matteodv99tn/MDM-Homework/Images/10-040.jpg

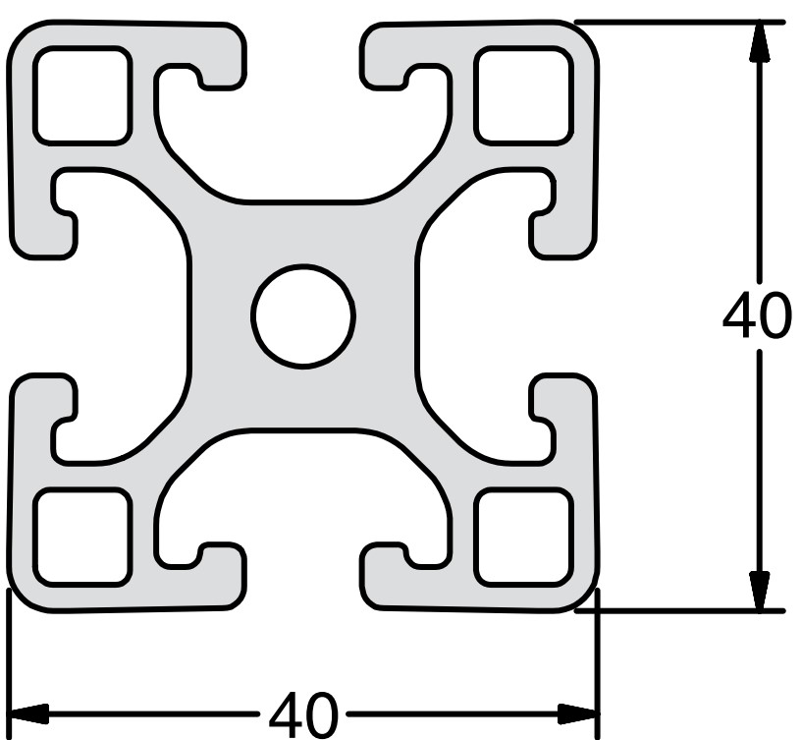
Images/10-040.jpg
