matteodv99tn/MDM-Homework/Images/10-080.jpg

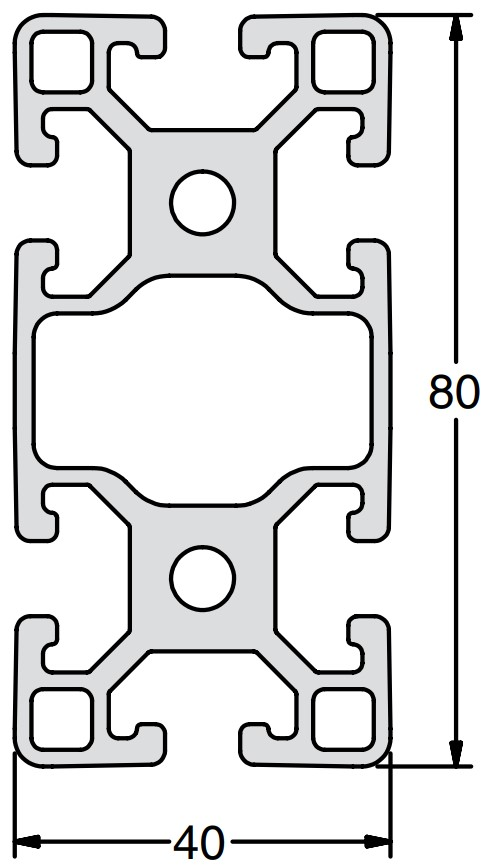
Images/10-080.jpg
