matteodv99tn/MDM-Homework/Images/10-540.jpg

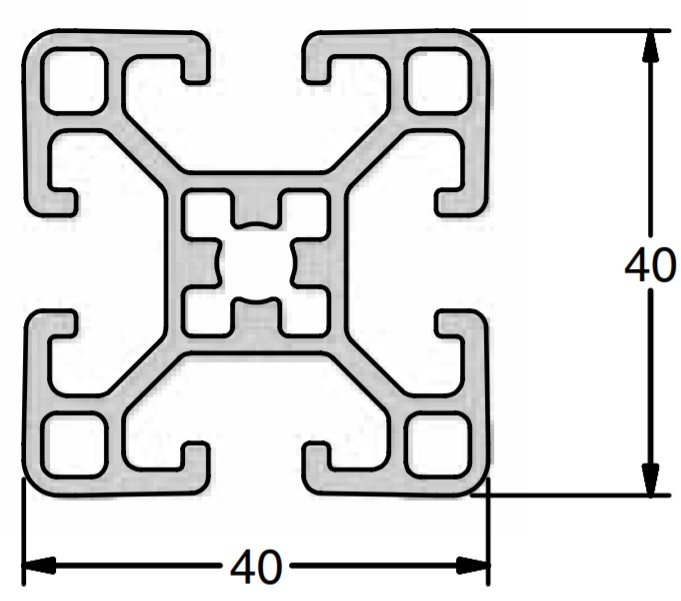
Images/10-540.jpg
