matteodv99tn/MDM-Homework/Images/11-040.jpg

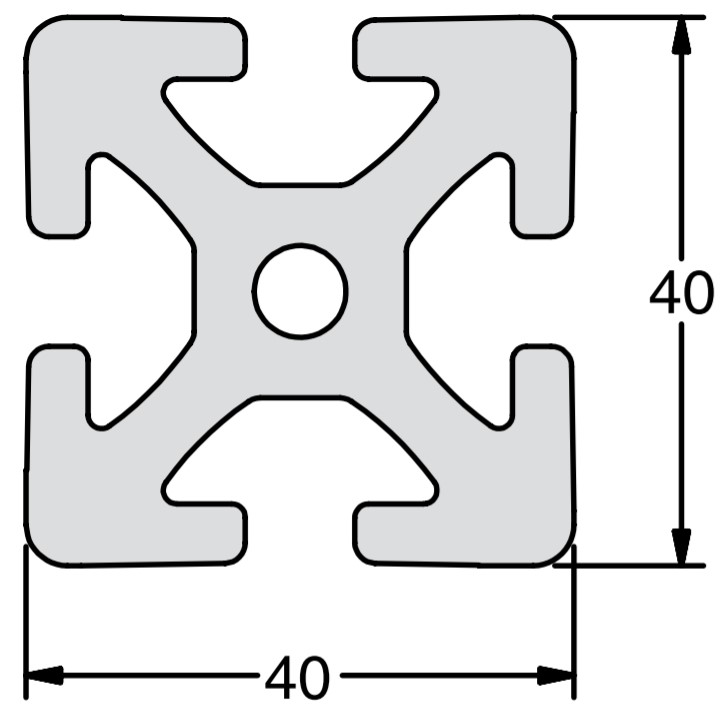
Images/11-040.jpg
