matteodv99tn/MDM-Homework/Images/gusset.png

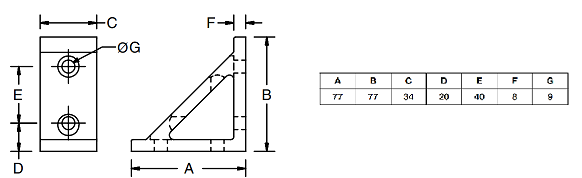
Images/gusset.png
