matteodv99tn/MDM-Homework/Images/pivot2.png

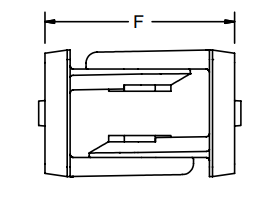
Images/pivot2.png
