matteodv99tn/MDM-Homework/Images/sectionD.png

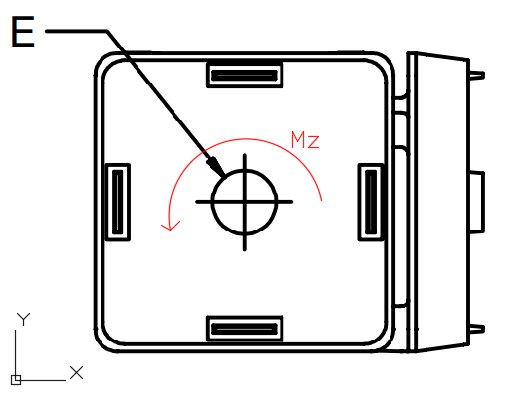
Images/sectionD.png
