matteodv99tn/MDM-Homework/Images/toothgear1.png

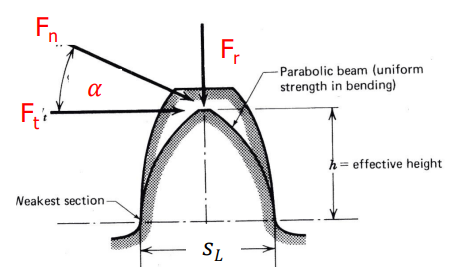
Images/toothgear1.png
