matteodv99tn/MDM-Homework/Images/toothgear2.png

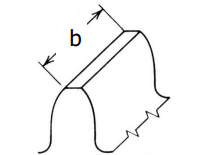
Images/toothgear2.png
