matteodv99tn/MDM-Homework/Images/xz.png

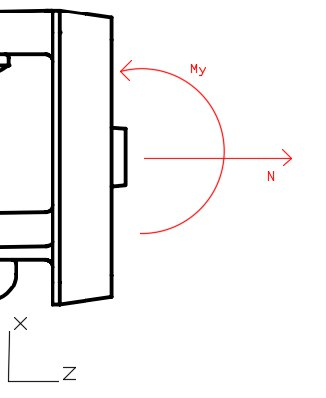
Images/xz.png
