matteodv99tn/MDM-Homework/Images/yz.png

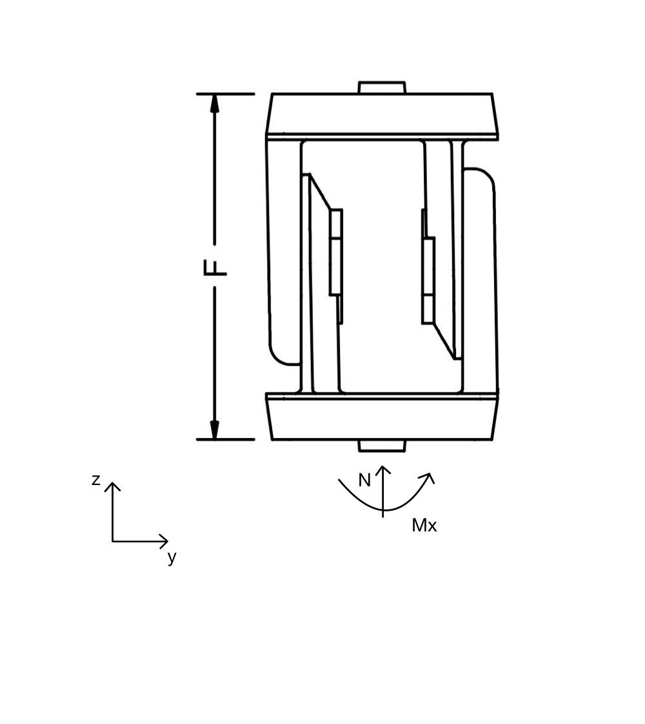
Images/yz.png
