matteodv99tn/MDM-Homework/Images/yzA_assex.png

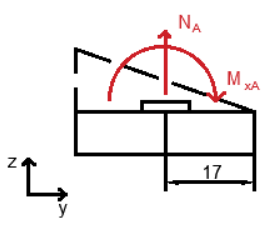
Images/yzA_assex.png
